ojousima/ieeeIV16/images/FFT-80_combined.jpg

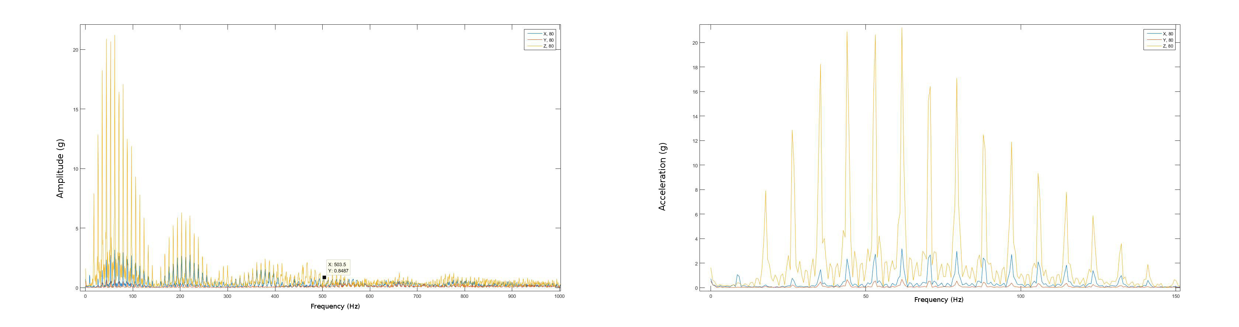
images/FFT-80_combined.jpg
