ojousima/ieeeIV16/images/Fig1.tif

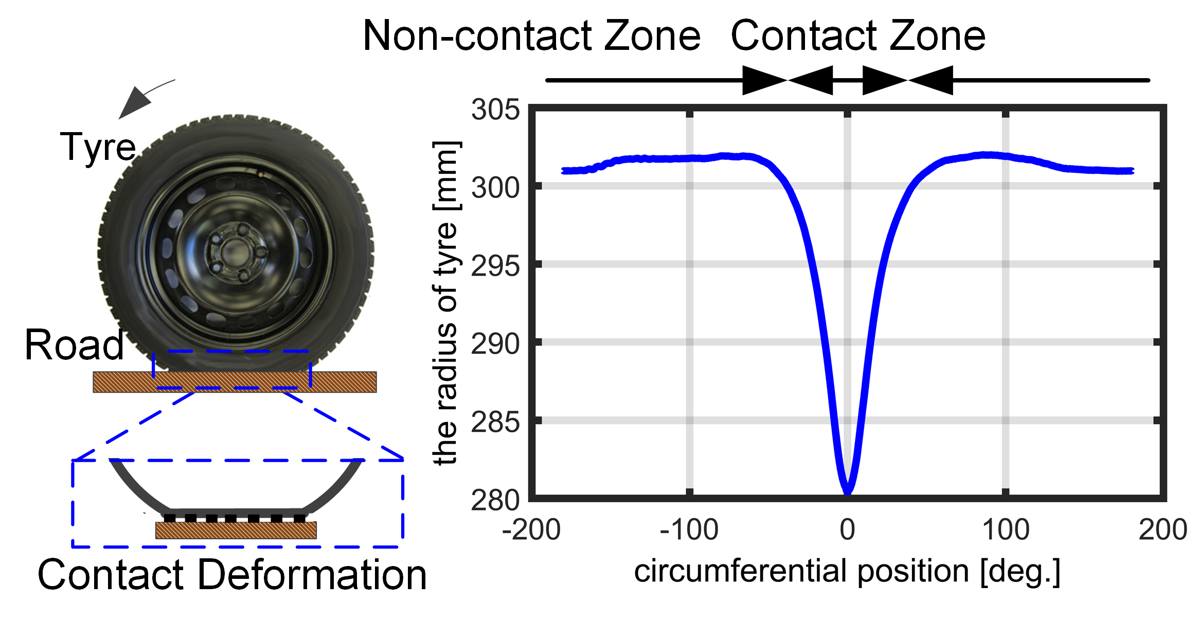
images/Fig1.tif
