ojousima/ieeeIV16/images/harvesting_circuit.jpg

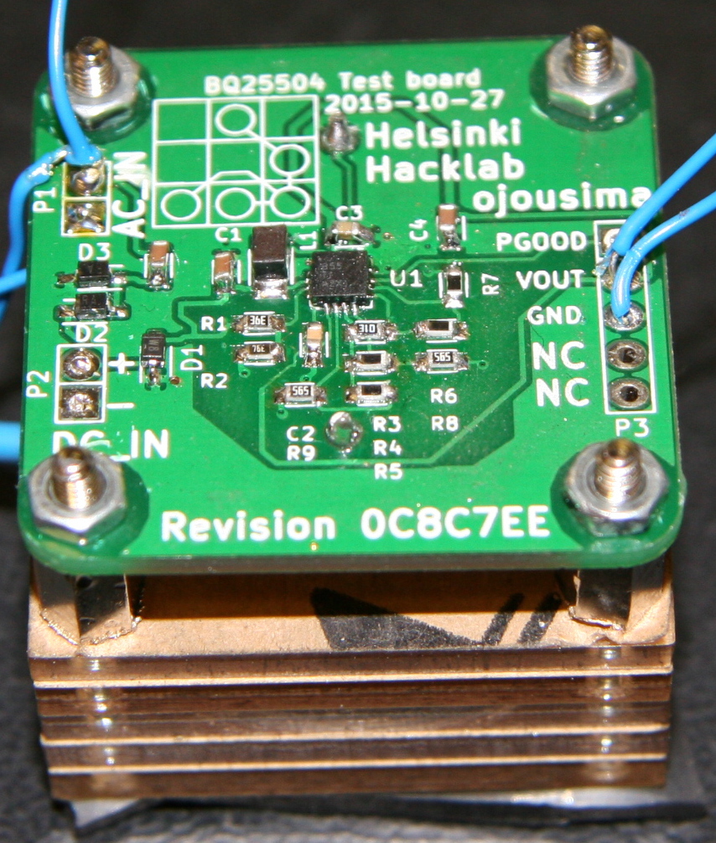
images/harvesting_circuit.jpg
