ojousima/ieeeIV16/images/mounting_dwg2.jpg

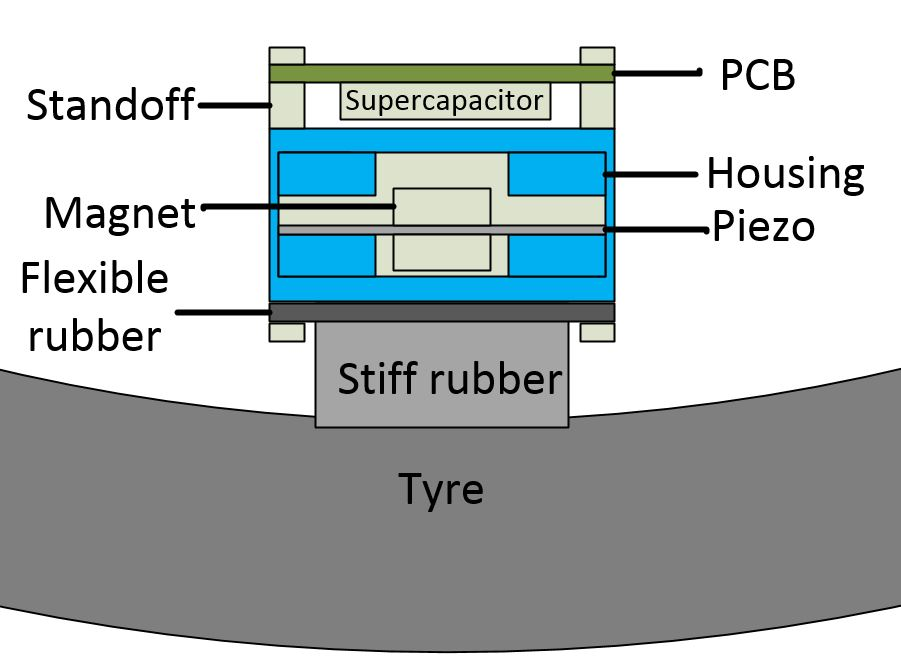
images/mounting_dwg2.jpg
