ojousima/ieeeIV16/images/piezo_td_open_330hz_2_2.png

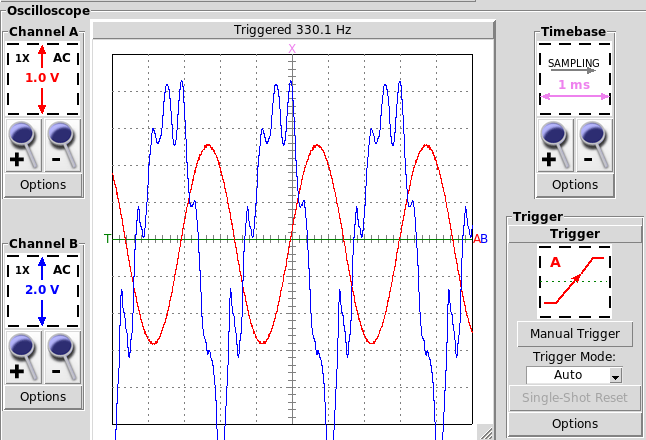
images/piezo_td_open_330hz_2_2.png
