ojousima/ieeeIV16/images/piezo_td_power_330hz_2_3.png

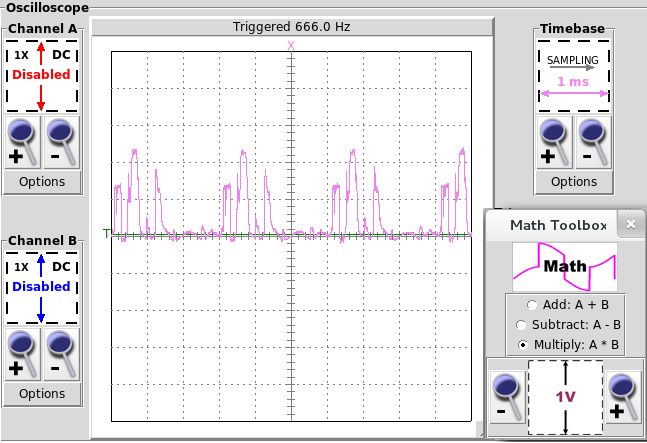
images/piezo_td_power_330hz_2_3.png
