ojousima/ieeeIV16/images/scap_discharge.png

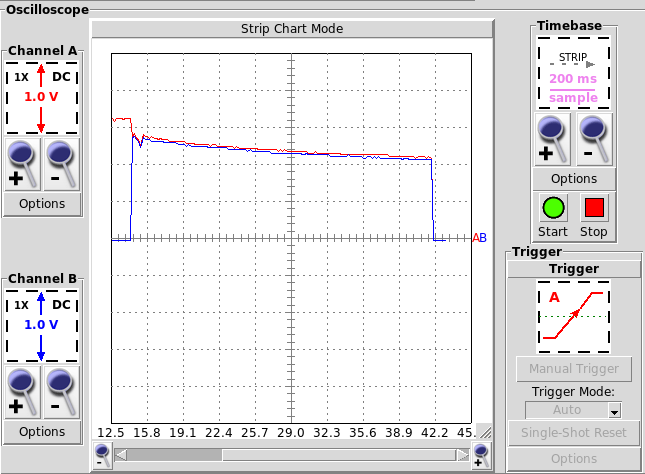
images/scap_discharge.png
